DhairyaAPImaster/60-Agni/Pics/Screenshot 2026-06-02 154645.png

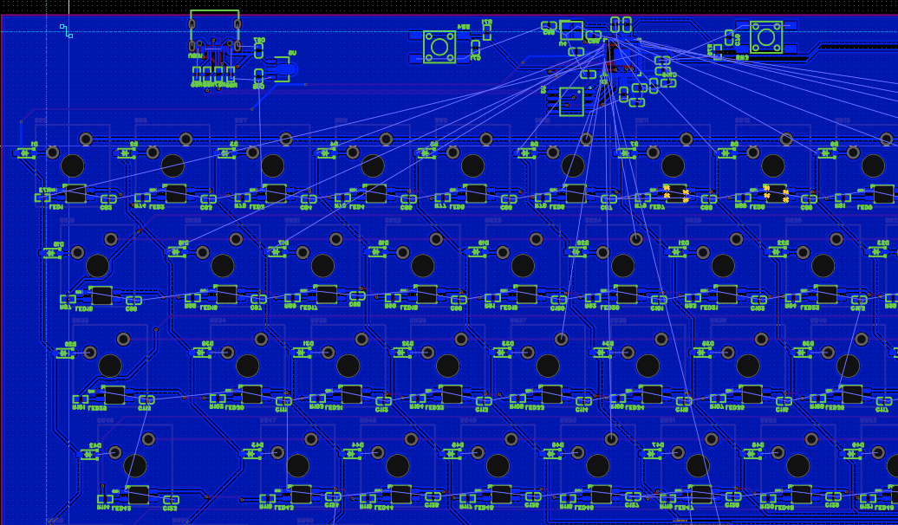
Pics/Screenshot 2026-06-02 154645.png
