DhairyaAPImaster/60-Agni/Pics/image (1).webp

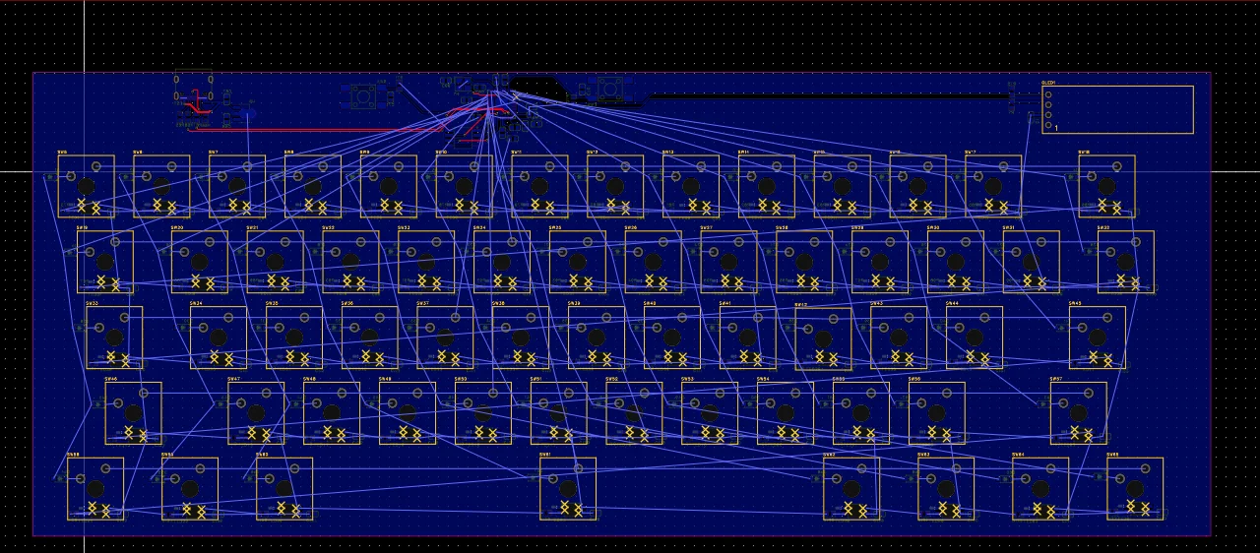
Pics/image (1).webp
