DhairyaAPImaster/60-Agni/Pics/image (2).webp

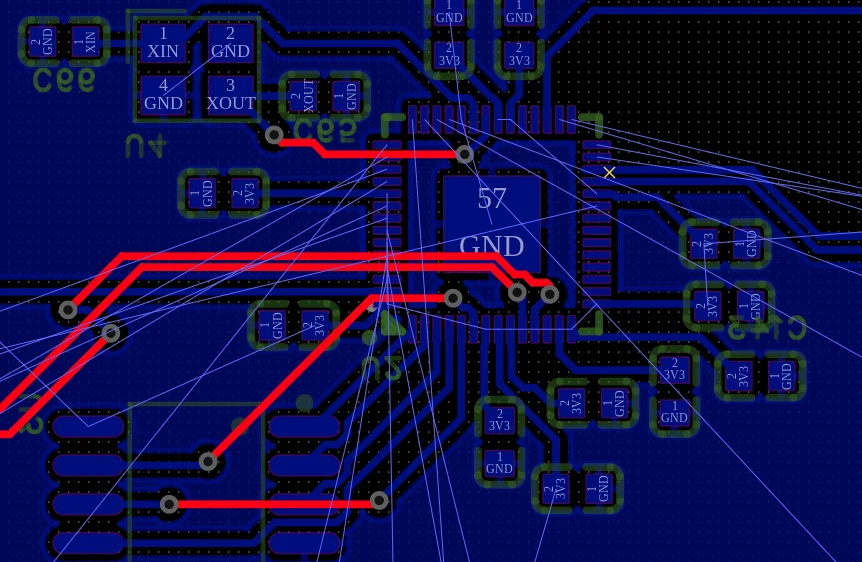
Pics/image (2).webp
