DhairyaAPImaster/60-Agni/Pics/image (4).webp

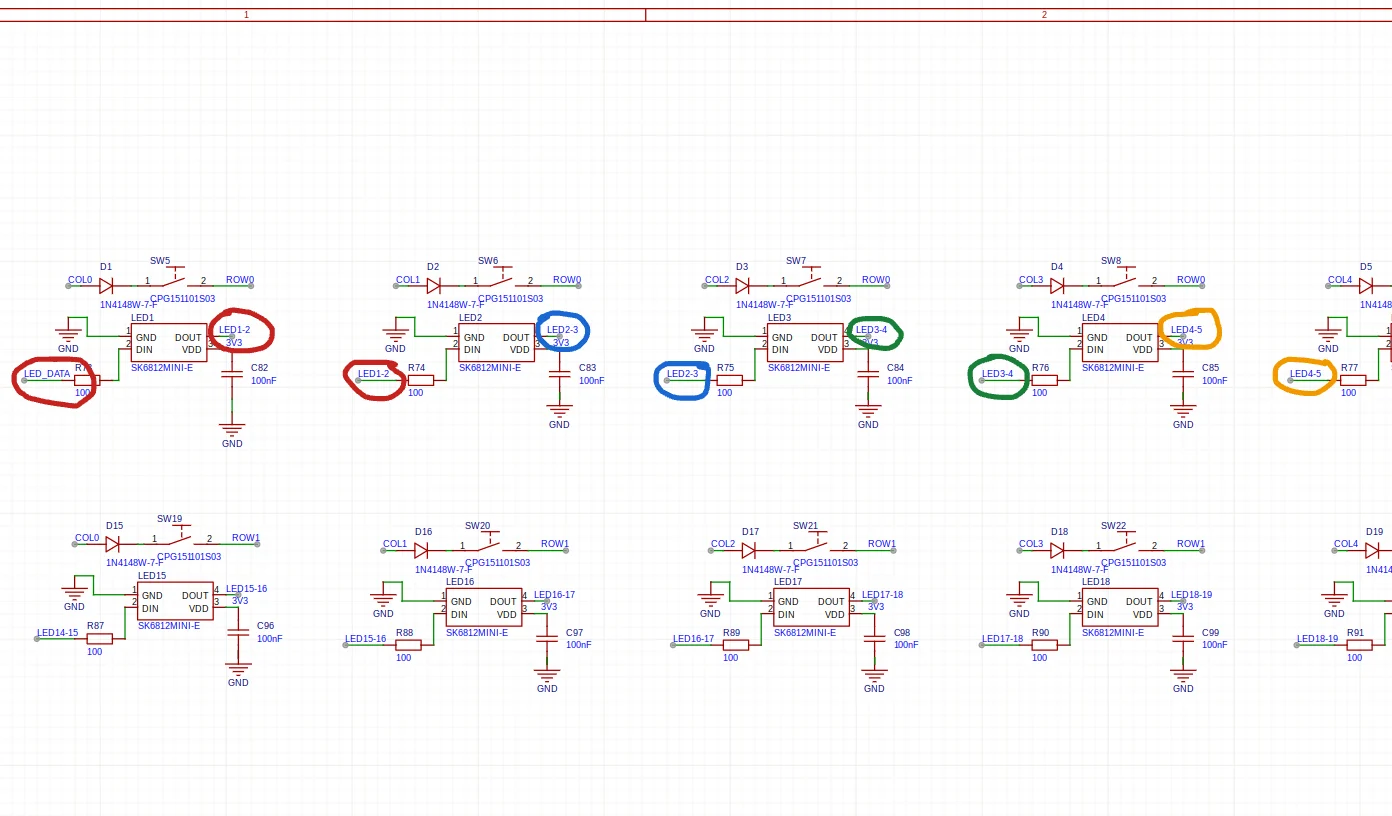
Pics/image (4).webp
