DhairyaAPImaster/60-Agni/Pics/image (5).webp

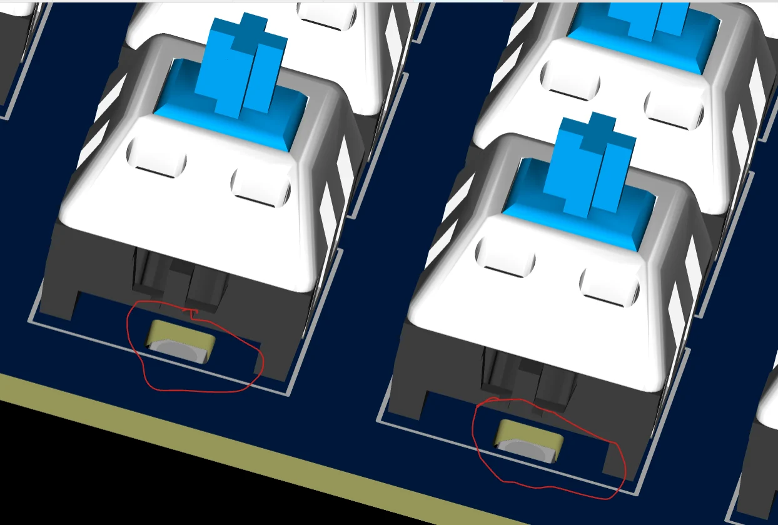
Pics/image (5).webp
