DhairyaAPImaster/60-Agni/Pics/image (6).webp

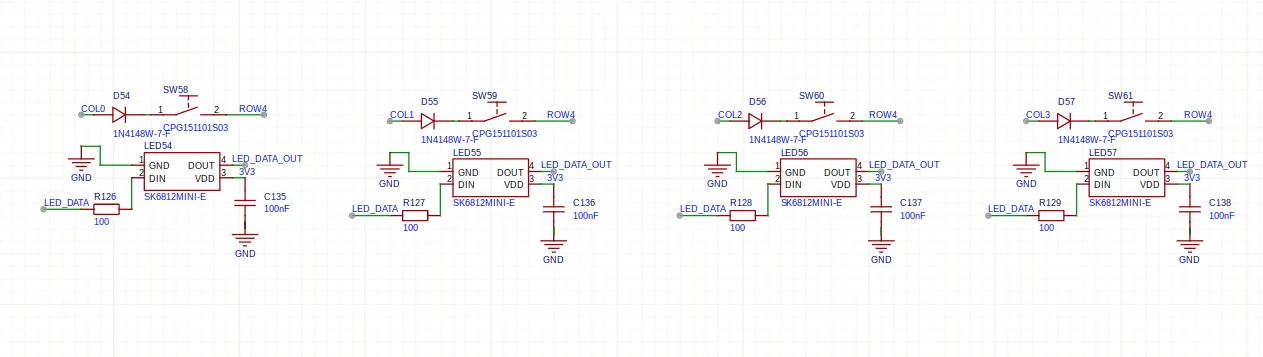
Pics/image (6).webp
