DhairyaAPImaster/60-Agni/Pics/image (7).webp

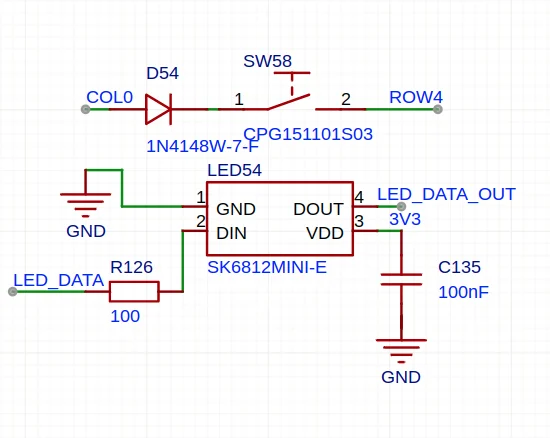
Pics/image (7).webp
