DhairyaAPImaster/60-Agni/Pics/image.png

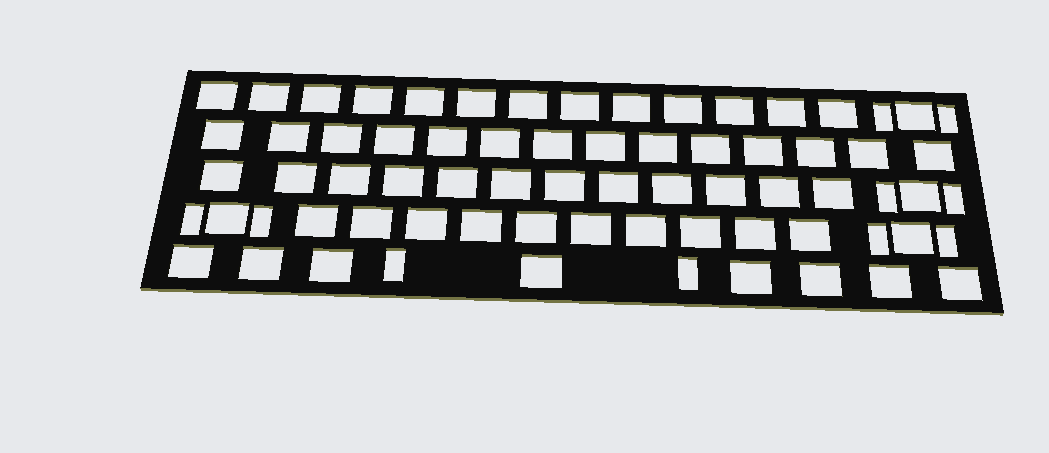
Pics/image.png
