DhairyaAPImaster/60-Agni/Pics/image.webp

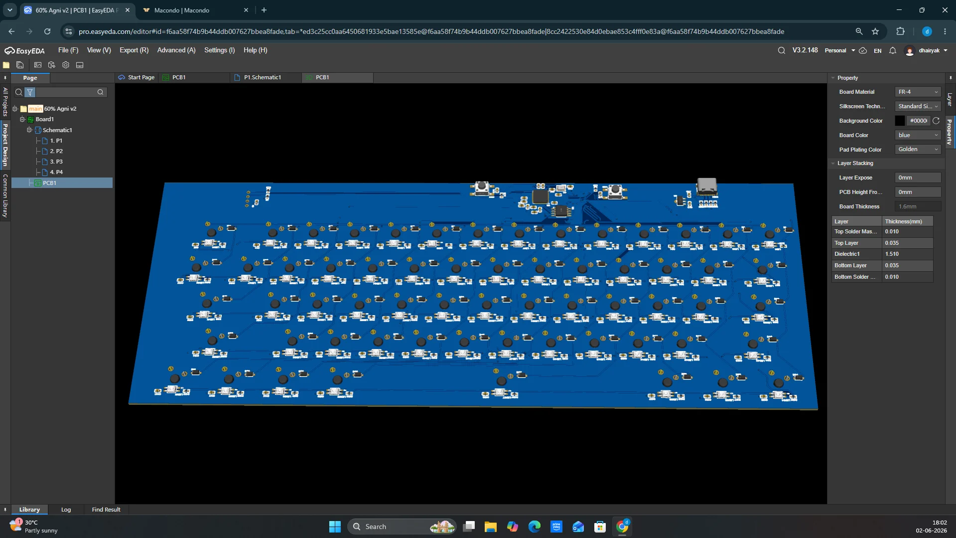
Pics/image.webp
