DhairyaAPImaster/60-Agni/Pics/Screenshot 2026-06-02 172739.png

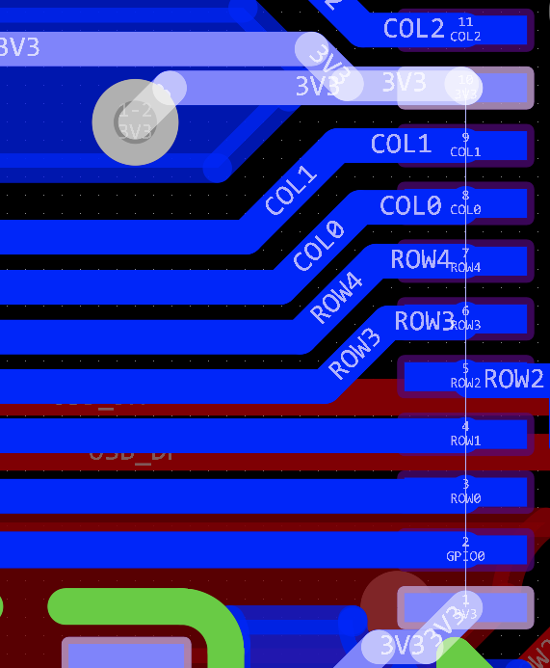
Pics/Screenshot 2026-06-02 172739.png
