DhairyaAPImaster/60-Agni/Pics/Screenshot 2026-06-02 180112.png

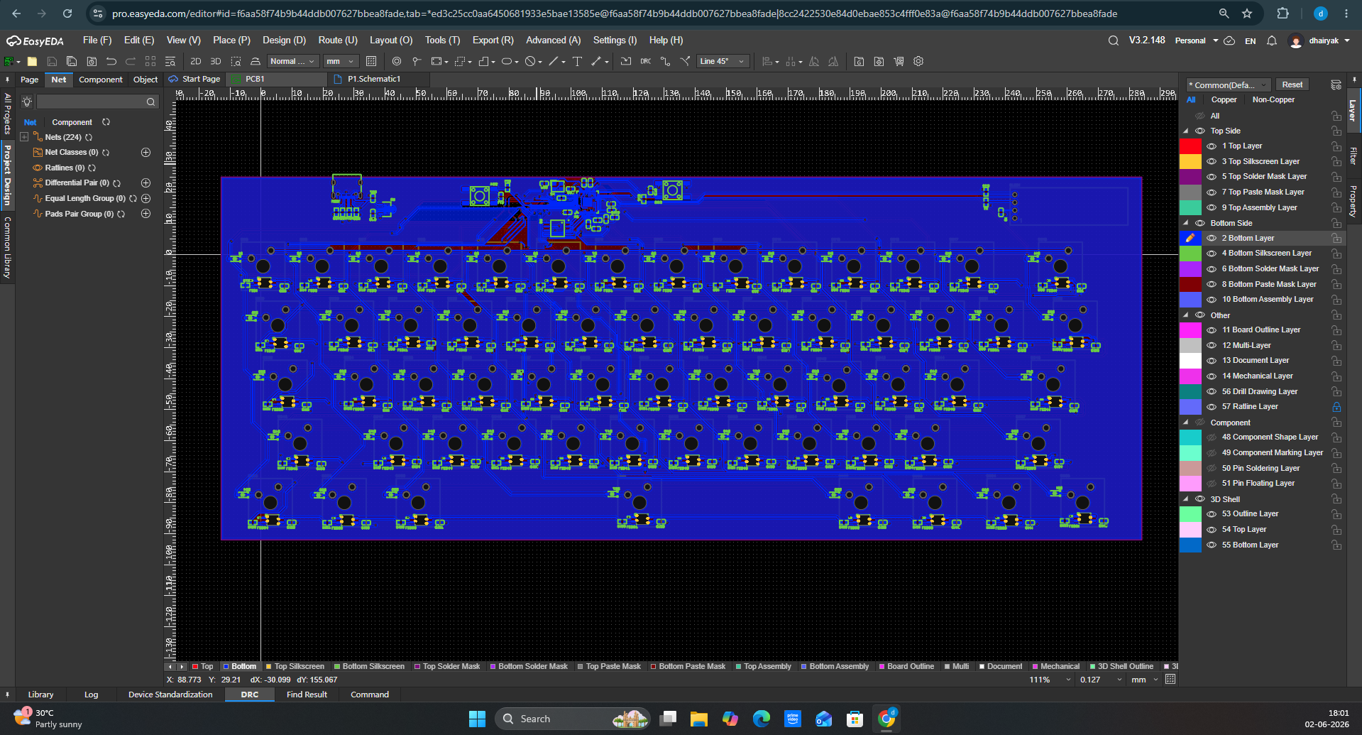
Pics/Screenshot 2026-06-02 180112.png
