DhairyaAPImaster/60-Agni/Pics/Screenshot 2026-06-02 180124.png

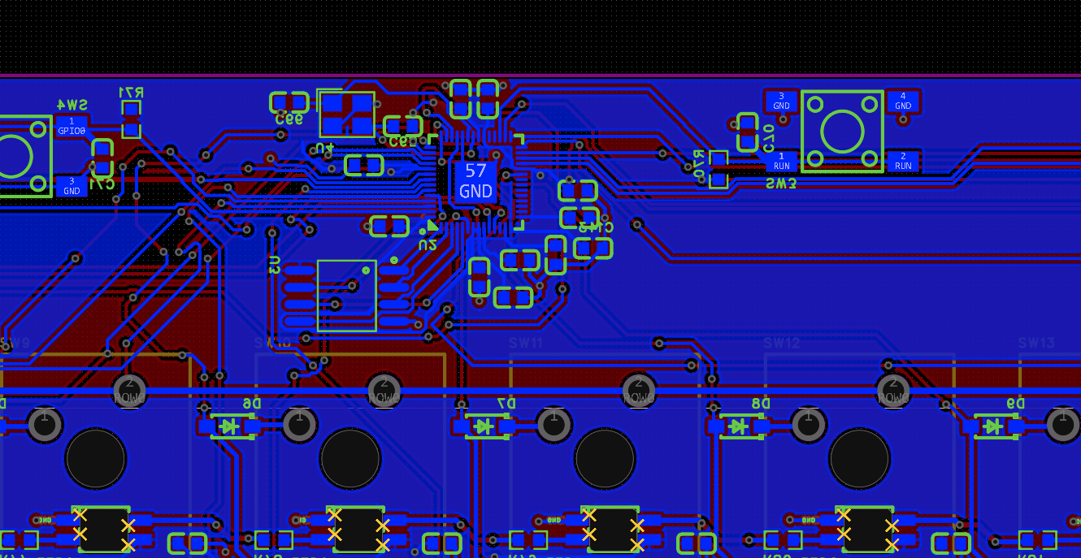
Pics/Screenshot 2026-06-02 180124.png
