DhairyaAPImaster/60-Agni/Pics/Screenshot 2026-06-02 180231.png

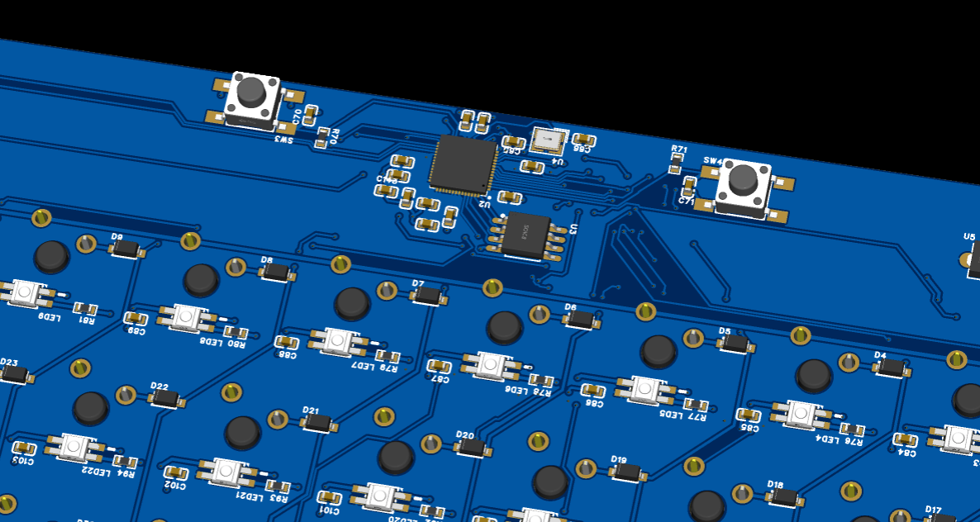
Pics/Screenshot 2026-06-02 180231.png
