DhairyaAPImaster/60-Agni/Pics/Screenshot 2026-06-02 182020.png

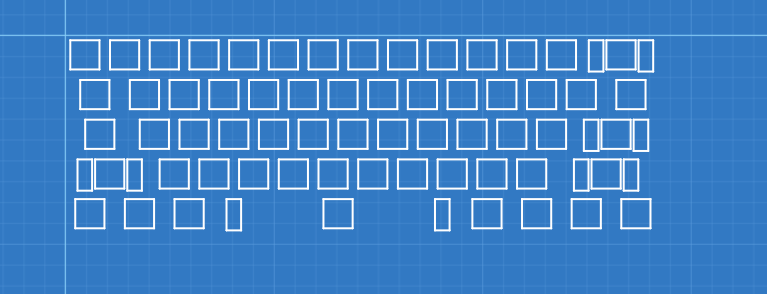
Pics/Screenshot 2026-06-02 182020.png
