DhairyaAPImaster/60-Agni/Pics/Screenshot 2026-06-04 154056.png

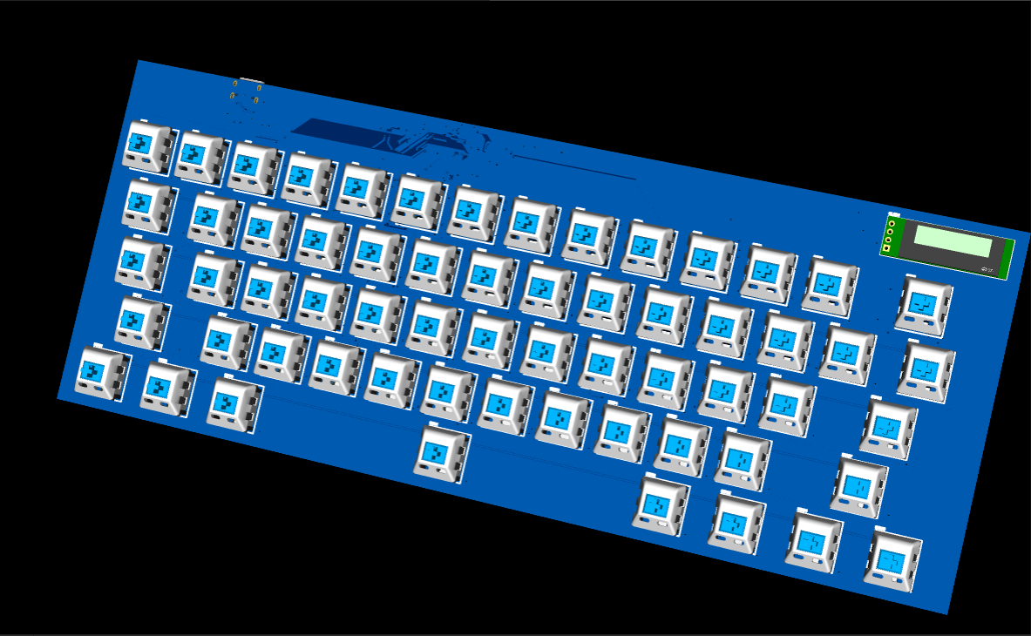
Pics/Screenshot 2026-06-04 154056.png
