DhairyaAPImaster/60-Agni/Pics/Screenshot 2026-06-04 155751.png

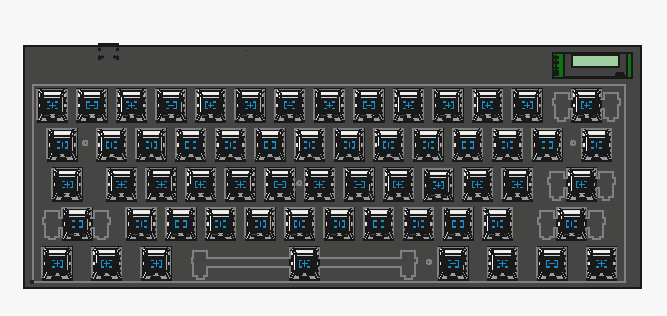
Pics/Screenshot 2026-06-04 155751.png
