DhairyaAPImaster/60-Agni/Pics/Screenshot 2026-06-04 155950.png

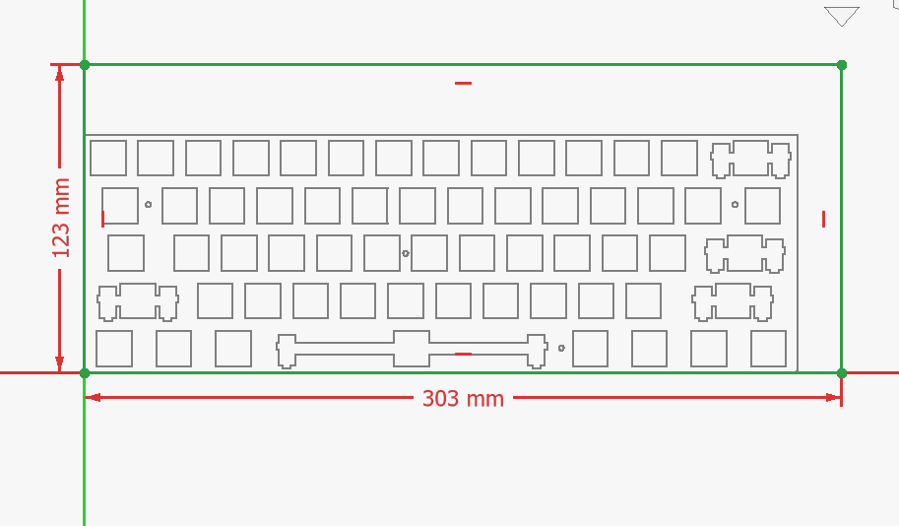
Pics/Screenshot 2026-06-04 155950.png
