DhairyaAPImaster/60-Agni/Pics/Screenshot 2026-06-04 165042.png

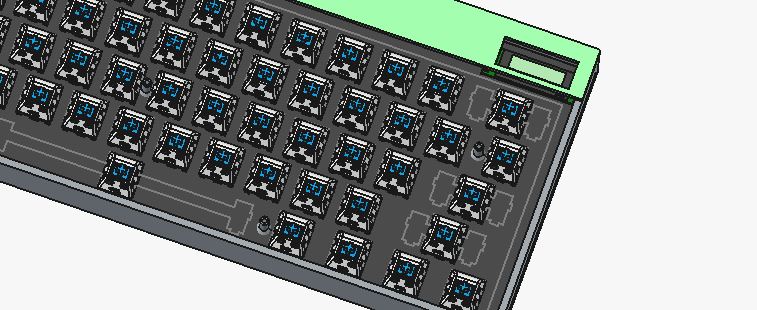
Pics/Screenshot 2026-06-04 165042.png
