DhairyaAPImaster/60-Agni/Pics/Screenshot 2026-06-04 171939.png

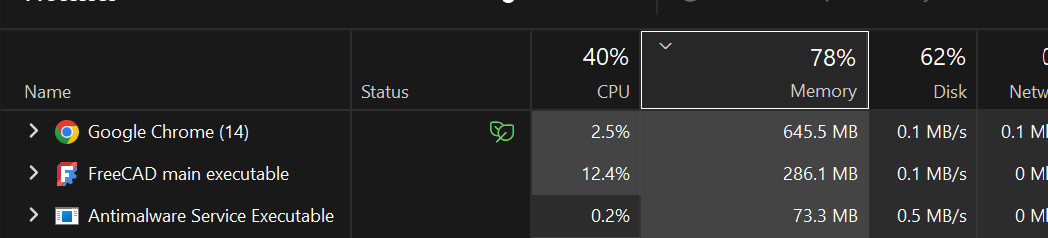
Pics/Screenshot 2026-06-04 171939.png
