DhairyaAPImaster/60-Agni/Pics/Screenshot 2026-06-04 173255.png

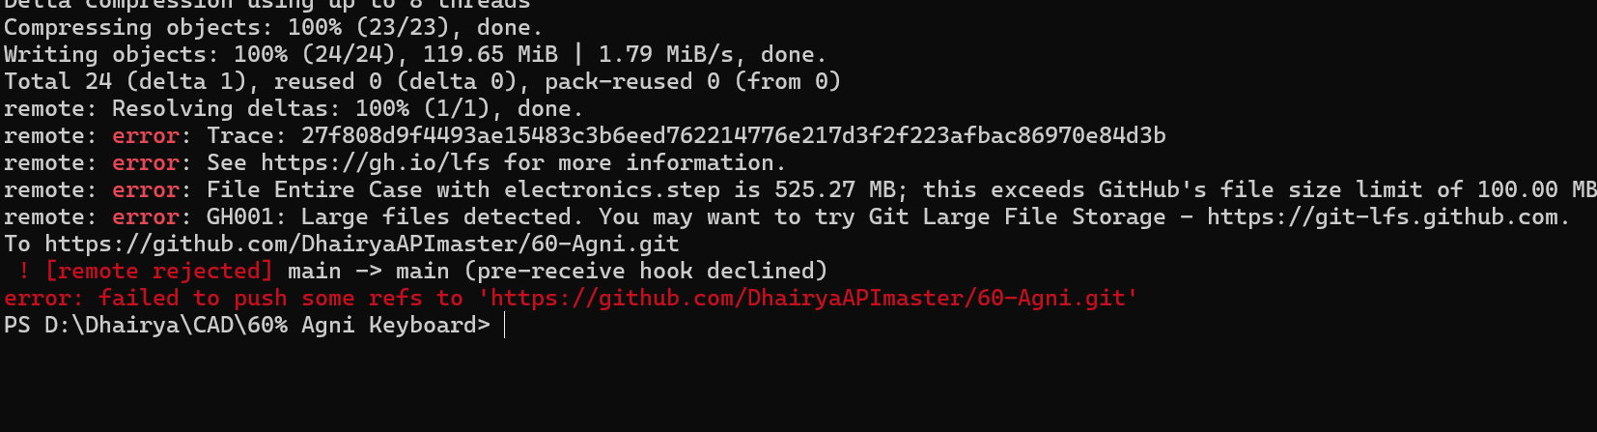
Pics/Screenshot 2026-06-04 173255.png
