DhairyaAPImaster/60-Agni/Pics/Screenshot 2026-06-05 220334.png

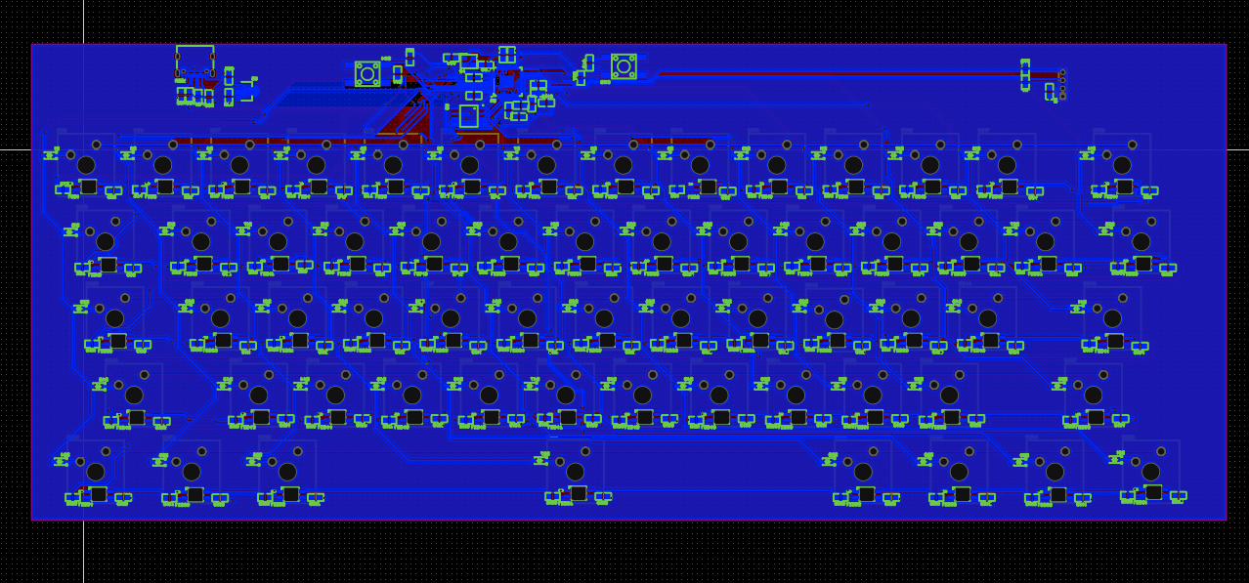
Pics/Screenshot 2026-06-05 220334.png
