DhairyaAPImaster/60-Agni/Pics/Screenshot 2026-06-05 223745.png

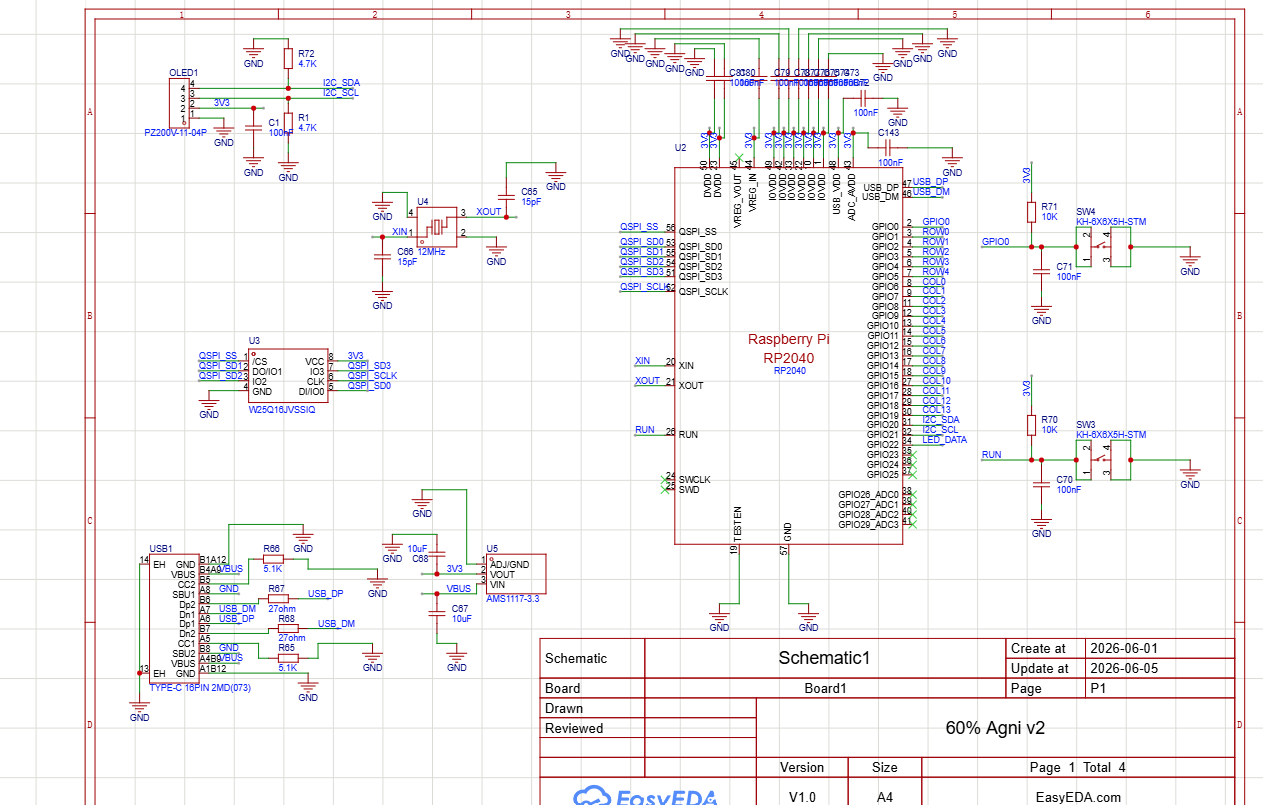
Pics/Screenshot 2026-06-05 223745.png
