DhairyaAPImaster/60-Agni/Pics/Screenshot 2026-06-05 223947.png

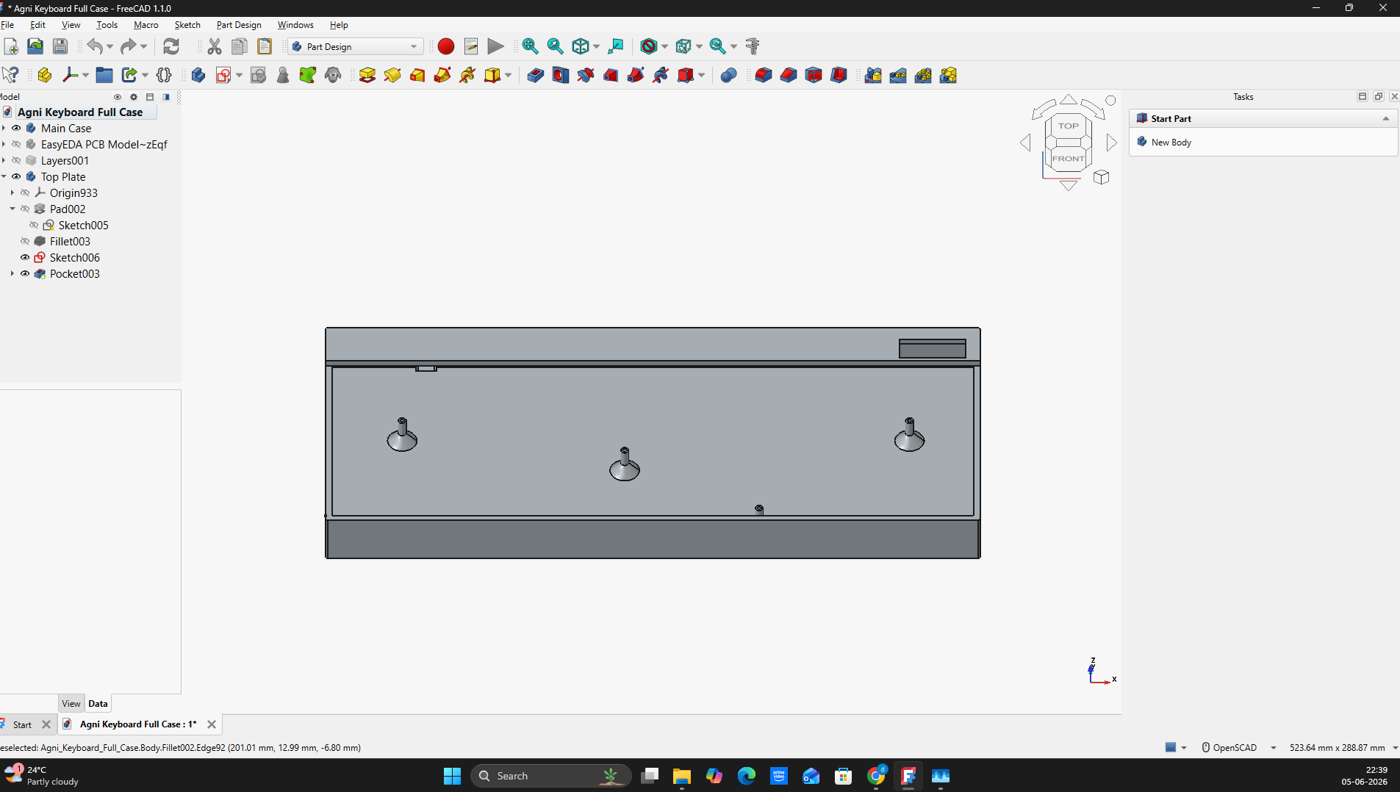
Pics/Screenshot 2026-06-05 223947.png
