DhairyaAPImaster/60-Agni/Pics/Screenshot 2026-06-05 224013.png

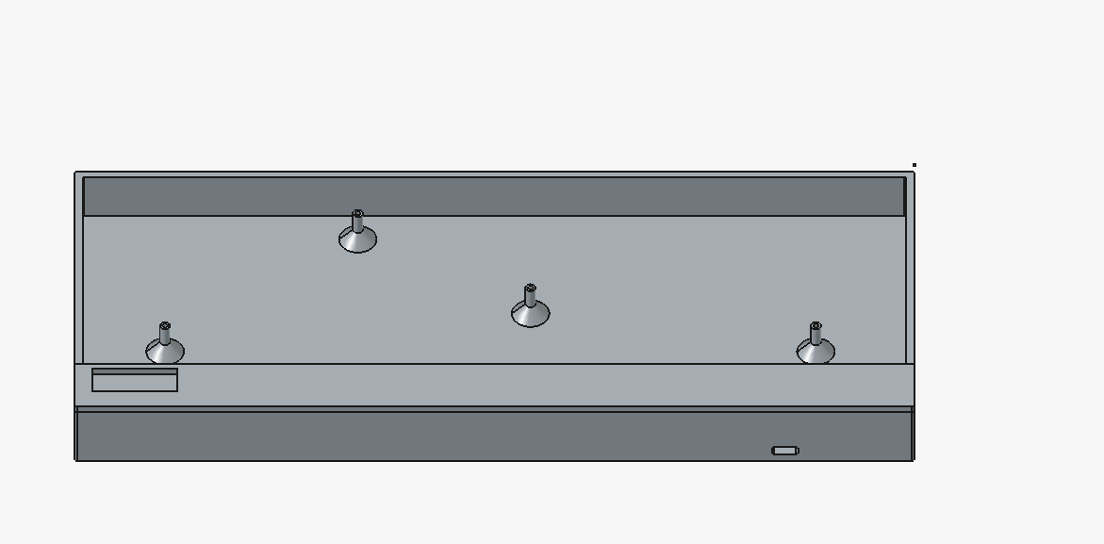
Pics/Screenshot 2026-06-05 224013.png
