DhairyaAPImaster/60-Agni/Pics/Screenshot 2026-06-05 224031.png

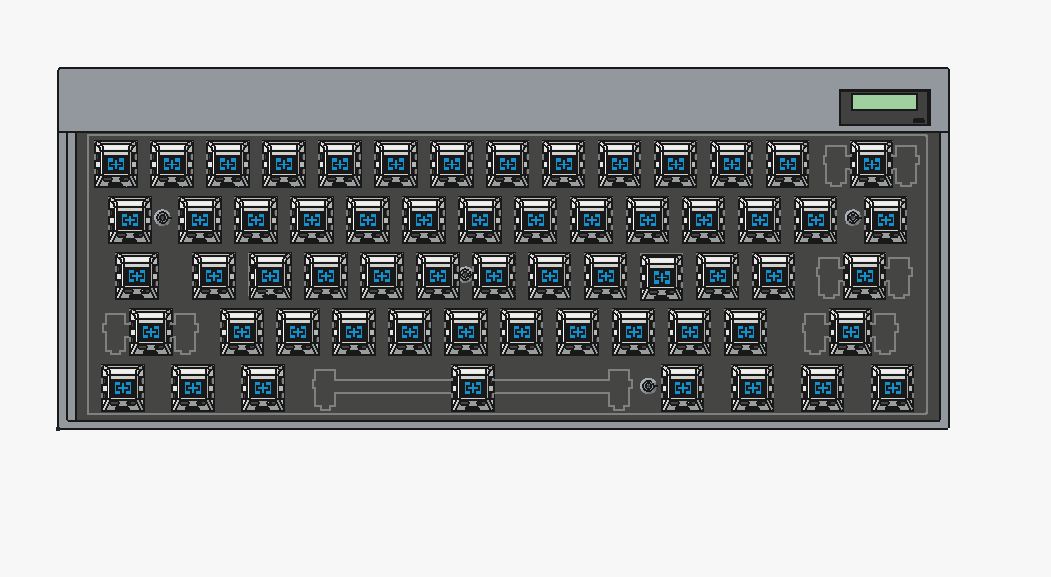
Pics/Screenshot 2026-06-05 224031.png
